greenonline/ATtiny_HVSP-ISP_stripboard/KiCAD_files/ATtiny_Dual_HVSP_ISP_Programmer/ATtiny_Dual_HVSP_ISP_Programmer.kicad_sch

## KiCad design KiCAD_files/ATtiny_Dual_HVSP_ISP_Programmer/ATtiny_Dual_HVSP_ISP_Programmer.kicad_sch (2023-06-02)

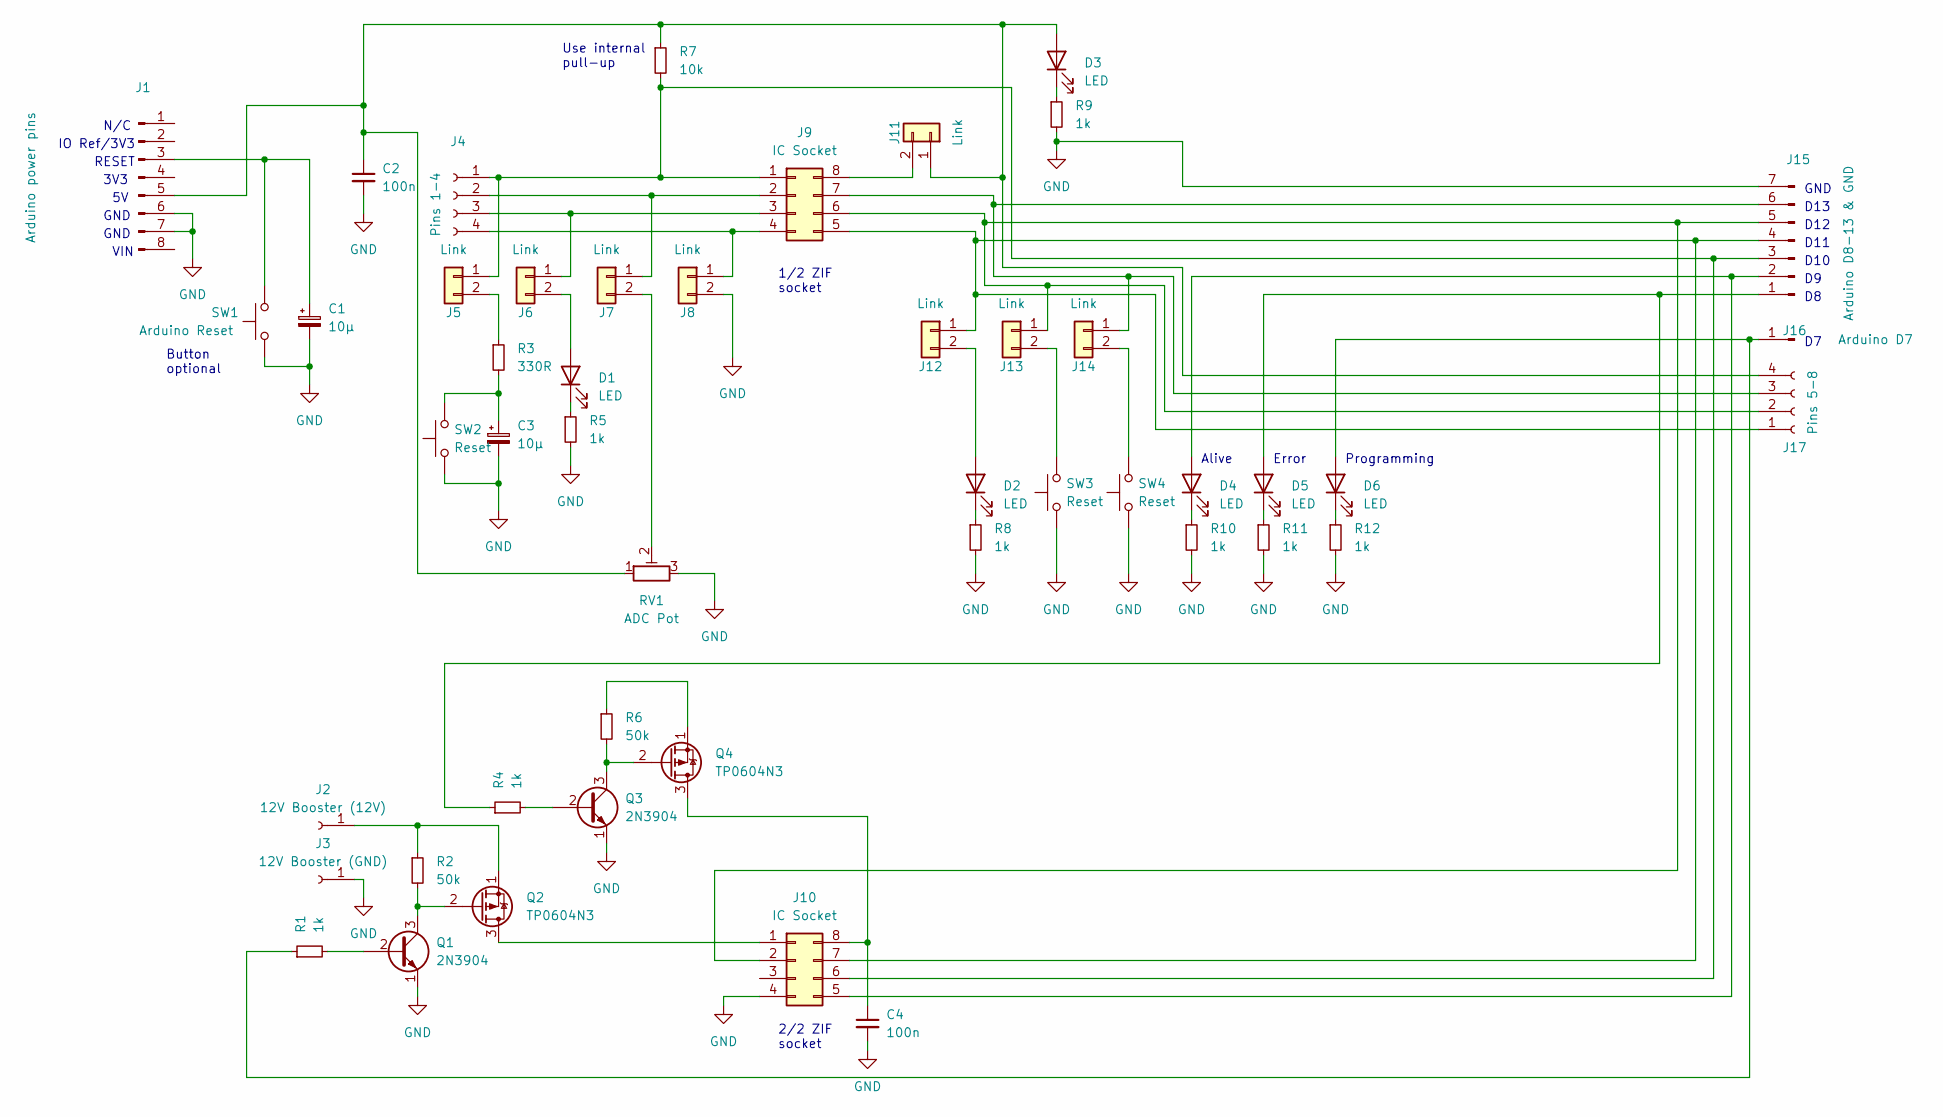
[picture p17: schematic ATtiny_Dual_HVSP_ISP_Programmer.kicad_sch]

Parts:
C1, C3: 10µ
C2, C4: 100n
D1, D2, D3, D4, D5, D6: LED
J1: Arduino power pins
J2: 12V Booster (12V)
J3: 12V Booster (GND)
J4: Pins 1-4
J5, J6, J7, J8, J11, J12, J13, J14: Link
J9, J10: IC Socket
J15: Arduino D8-13 & GND
J16: Arduino D7
J17: Pins 5-8
Q1, Q3: 2N3904; TO-92_Inline
Q2, Q4: TP0604N3; TO-92L_Inline
R1, R4, R5, R8, R9, R10, R11, R12: 1k
R2, R6: 50k
R3: 330R
R7: 10k
RV1: ADC Pot
SW1: Arduino Reset
SW2, SW3, SW4: Reset

Connections:
GND: C1.2, C2.2, C3.2, C4.2, J1.6, J1.7, J3.1, J8.2, J10.4, J15.7, Q1.1 (E), Q3.1 (E), R5.2, R8.2, R9.2, R10.2, R11.2, R12.2, RV1.3, SW1.1, SW2.1, SW3.1, SW4.1
unnamed: C1.1, J1.3, SW1.2
unnamed: C2.1, D3.2 (A), J1.5, J11.1, J17.4, R7.1, RV1.1
unnamed: C3.1, R3.2, SW2.2
unnamed: C4.1, J10.8, Q4.3 (D)
unnamed: D1.1 (K), R5.1
unnamed: D1.2 (A), J6.2
unnamed: D2.1 (K), R8.1
unnamed: D2.2 (A), J12.2
unnamed: D3.1 (K), R9.1
unnamed: D4.1 (K), R10.1
unnamed: D4.2 (A), J10.5, J15.2
unnamed: D5.1 (K), R11.1
unnamed: D5.2 (A), J15.1, R4.1
unnamed: D6.1 (K), R12.1
unnamed: D6.2 (A), J16.1, R1.1
unnamed: J2.1, Q2.1 (S), R2.1
unnamed: J4.2, J7.1, J9.2
unnamed: J4.3, J6.1, J9.3
unnamed: J4.4, J8.1, J9.4
unnamed: J5.2, R3.1
unnamed: J7.2, RV1.2
unnamed: J10.1, Q2.3 (D)
unnamed: J9.6, J10.2, J13.1, J15.5, J17.2
unnamed: J4.1, J5.1, J9.1, J10.6, J15.3, R7.2
unnamed: J9.5, J10.7, J12.1, J15.4, J17.1
unnamed: J9.8, J11.2
unnamed: J13.2, SW3.2
unnamed: J9.7, J14.1, J15.6, J17.3
unnamed: J14.2, SW4.2
unnamed: Q1.2 (B), R1.2
unnamed: Q1.3 (C), Q2.2 (G), R2.2
unnamed: Q3.2 (B), R4.2
unnamed: Q3.3 (C), Q4.2 (G), R6.2
unnamed: Q4.1 (S), R6.1

Notes on the sheet:
VIN
2/2 ZIF socket
N/C
D13
GND
D10
1/2 ZIF socket
Programming
Button optional
RESET
D12
Error
Alive
3V3
D11
Use internal pull-up
IO Ref/3V3
