greenonline/ATtiny_HVSP-ISP_stripboard/KiCAD_files/ATtiny_Dual_HVSP_ISP_Programmer/ATtiny_Dual_HVSP_ISP_Programmer_(ISP_Only).kicad_sch

## KiCad design KiCAD_files/ATtiny_Dual_HVSP_ISP_Programmer/ATtiny_Dual_HVSP_ISP_Programmer_(ISP_Only).kicad_sch (2023-06-02)

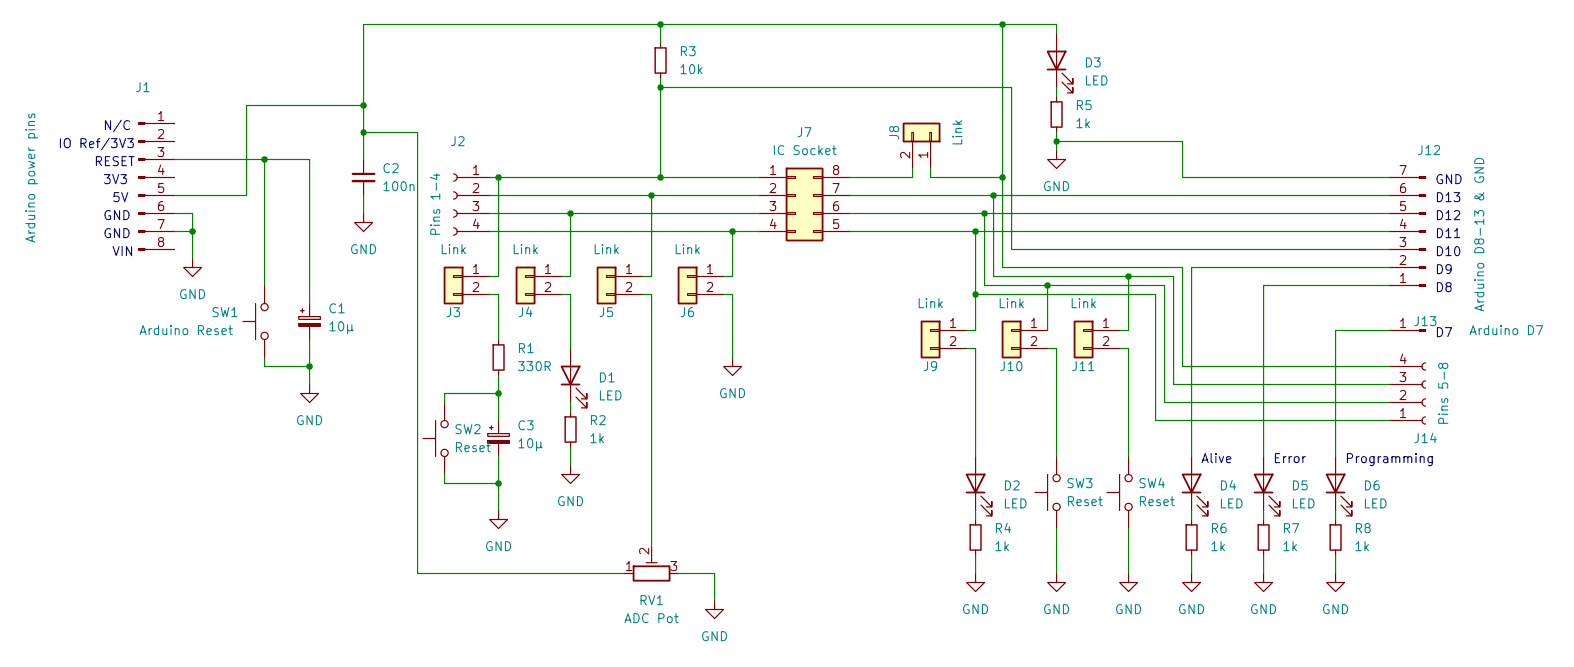
[picture p18: schematic ATtiny_Dual_HVSP_ISP_Programmer_(ISP_Only).kicad_sch]

Parts:
C1, C3: 10µ
C2: 100n
D1, D2, D3, D4, D5, D6: LED
J1: Arduino power pins
J2: Pins 1-4
J3, J4, J5, J6, J8, J9, J10, J11: Link
J7: IC Socket
J12: Arduino D8-13 & GND
J13: Arduino D7
J14: Pins 5-8
R1: 330R
R2, R4, R5, R6, R7, R8: 1k
R3: 10k
RV1: ADC Pot
SW1: Arduino Reset
SW2, SW3, SW4: Reset

Connections:
GND: C1.2, C2.2, C3.2, J1.6, J1.7, J6.2, J12.7, R2.2, R4.2, R5.2, R6.2, R7.2, R8.2, RV1.3, SW1.1, SW2.1, SW3.1, SW4.1
unnamed: C1.1, J1.3, SW1.2
unnamed: C2.1, D3.2 (A), J1.5, J8.1, J14.4, R3.1, RV1.1
unnamed: C3.1, R1.2, SW2.2
unnamed: D1.1 (K), R2.1
unnamed: D1.2 (A), J4.2
unnamed: D2.1 (K), R4.1
unnamed: D2.2 (A), J9.2
unnamed: D3.1 (K), R5.1
unnamed: D4.1 (K), R6.1
unnamed: D4.2 (A), J12.2
unnamed: D5.1 (K), R7.1
unnamed: D5.2 (A), J12.1
unnamed: D6.1 (K), R8.1
unnamed: D6.2 (A), J13.1
unnamed: J2.2, J5.1, J7.2
unnamed: J2.3, J4.1, J7.3
unnamed: J2.4, J6.1, J7.4
unnamed: J3.2, R1.1
unnamed: J5.2, RV1.2
unnamed: J7.8, J8.2
unnamed: J7.6, J10.1, J12.5, J14.2
unnamed: J10.2, SW3.2
unnamed: J7.7, J11.1, J12.6, J14.3
unnamed: J11.2, SW4.2
unnamed: J2.1, J3.1, J7.1, J12.3, R3.2
unnamed: J7.5, J9.1, J12.4, J14.1

Notes on the sheet:
VIN
N/C
D13
GND
D10
Programming
RESET
D12
Error
Alive
3V3
D11
IO Ref/3V3
