greenonline/ATtiny_HVSP-ISP_stripboard/KiCAD_files/ATtiny_Dual_HVSP_ISP_Programmer_with_MAX662A(+)/ATtiny_Dual_HVSP_ISP_Programmer_with_MAX662.kicad_sch

## KiCad design KiCAD_files/ATtiny_Dual_HVSP_ISP_Programmer_with_MAX662A(+)/ATtiny_Dual_HVSP_ISP_Programmer_with_MAX662.kicad_sch (2023-06-12)

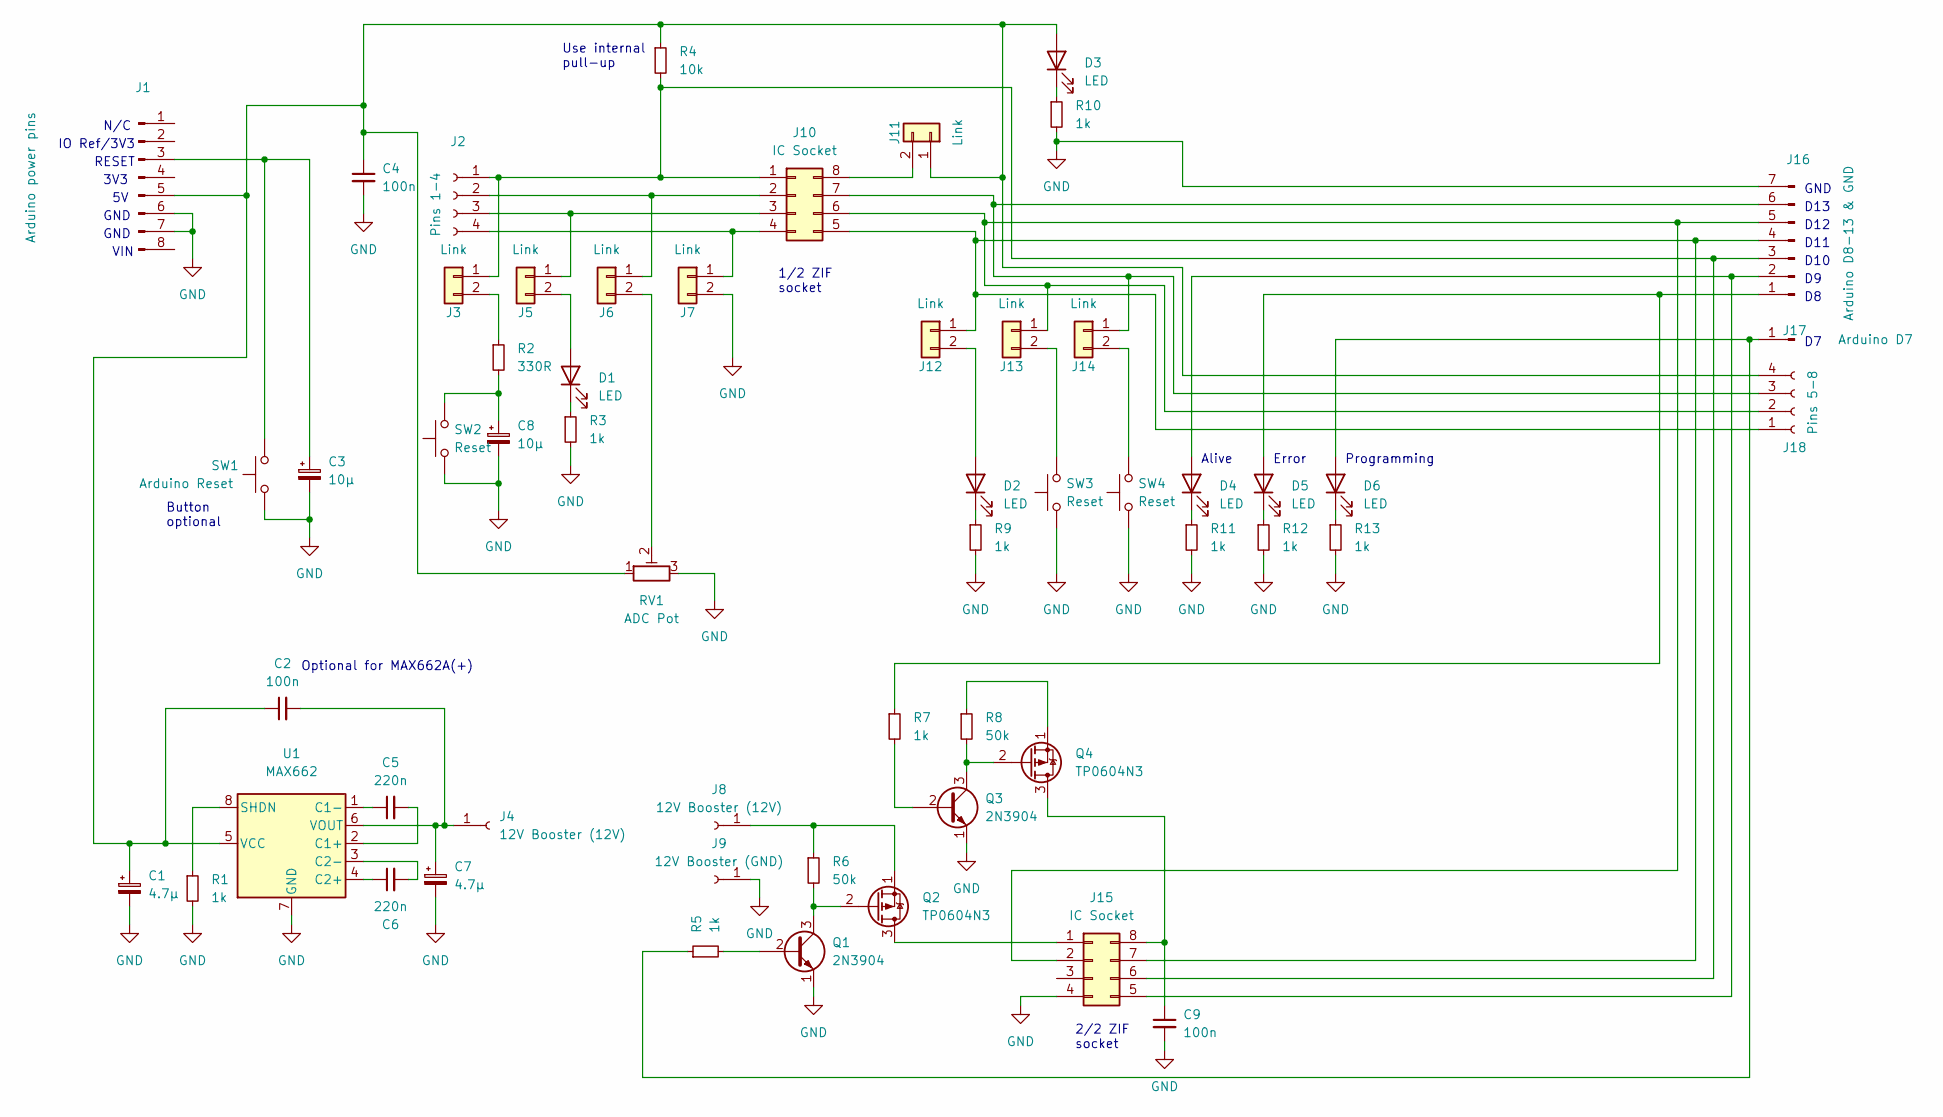
[picture p19: schematic ATtiny_Dual_HVSP_ISP_Programmer_with_MAX662.kicad_sch]

Parts:
C1, C7: 4.7µ
C2, C4, C9: 100n
C3, C8: 10µ
C5, C6: 220n
D1, D2, D3, D4, D5, D6: LED
J1: Arduino power pins
J2: Pins 1-4
J3, J5, J6, J7, J11, J12, J13, J14: Link
J4, J8: 12V Booster (12V)
J9: 12V Booster (GND)
J10, J15: IC Socket
J16: Arduino D8-13 & GND
J17: Arduino D7
J18: Pins 5-8
Q1, Q3: 2N3904; TO-92_Inline
Q2, Q4: TP0604N3; TO-92L_Inline
R1, R3, R5, R7, R9, R10, R11, R12, R13: 1k
R2: 330R
R4: 10k
R6, R8: 50k
RV1: ADC Pot
SW1: Arduino Reset
SW2, SW3, SW4: Reset
U1: MAX662

Connections:
GND: C1.2, C3.2, C4.2, C7.2, C8.2, C9.2, J1.6, J1.7, J7.2, J9.1, J15.4, J16.7, Q1.1 (E), Q3.1 (E), R1.2, R3.2, R9.2, R10.2, R11.2, R12.2, R13.2, RV1.3, SW1.1, SW2.1, SW3.1, SW4.1, U1.7 (GND)
unnamed: C1.1, C2.1, C4.1, D3.2 (A), J1.5, J11.1, J18.4, R4.1, RV1.1, U1.5 (VCC)
unnamed: C2.2, C7.1, J4.1, U1.6 (VOUT)
unnamed: C3.1, J1.3, SW1.2
unnamed: C5.1, U1.1 (C1-)
unnamed: C5.2, U1.2 (C1+)
unnamed: C6.1, U1.4 (C2+)
unnamed: C6.2, U1.3 (C2-)
unnamed: C8.1, R2.2, SW2.2
unnamed: C9.1, J15.8, Q4.3 (D)
unnamed: D1.1 (K), R3.1
unnamed: D1.2 (A), J5.2
unnamed: D2.1 (K), R9.1
unnamed: D2.2 (A), J12.2
unnamed: D3.1 (K), R10.1
unnamed: D4.1 (K), R11.1
unnamed: D4.2 (A), J15.5, J16.2
unnamed: D5.1 (K), R12.1
unnamed: D5.2 (A), J16.1, R7.1
unnamed: D6.1 (K), R13.1
unnamed: D6.2 (A), J17.1, R5.1
unnamed: J3.2, R2.1
unnamed: J6.2, RV1.2
unnamed: J8.1, Q2.1 (S), R6.1
unnamed: J2.1, J3.1, J10.1, J15.6, J16.3, R4.2
unnamed: J2.2, J6.1, J10.2
unnamed: J2.3, J5.1, J10.3
unnamed: J2.4, J7.1, J10.4
unnamed: J10.5, J12.1, J15.7, J16.4, J18.1
unnamed: J10.6, J13.1, J15.2, J16.5, J18.2
unnamed: J10.7, J14.1, J16.6, J18.3
unnamed: J10.8, J11.2
unnamed: J13.2, SW3.2
unnamed: J14.2, SW4.2
unnamed: J15.1, Q2.3 (D)
unnamed: Q1.2 (B), R5.2
unnamed: Q1.3 (C), Q2.2 (G), R6.2
unnamed: Q3.2 (B), R7.2
unnamed: Q3.3 (C), Q4.2 (G), R8.2
unnamed: Q4.1 (S), R8.1
unnamed: R1.1, U1.8 (SHDN)

Notes on the sheet:
VIN
2/2 ZIF socket
N/C
D13
Optional for MAX662A(+)
GND
D10
1/2 ZIF socket
Programming
Button optional
RESET
D12
Error
Alive
3V3
D11
Use internal pull-up
IO Ref/3V3
